mhiuuu/corny/3D/V1/left_case.step

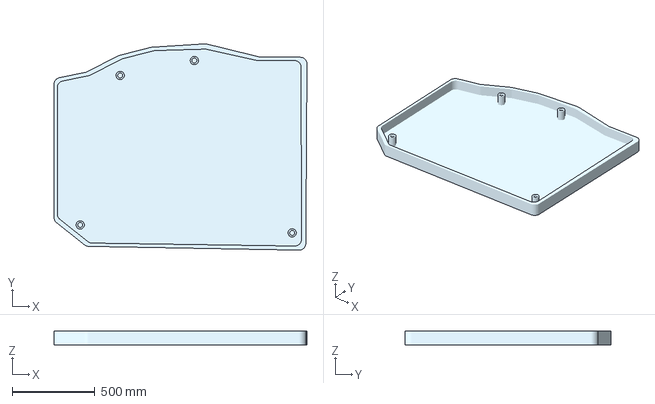
[picture p24: CAD file, 2025-06-06, an earlier design]
3D/V1/left_case.step
1525.2 x 1243.7 x 84.0 mm
